Metalchocobo/minu-bench-scale/docs/mechanical/prototype-affordability/ready-made-frames.md

# Telai commerciali per un solo prototipo economico

La candidatura principale corrente è il [gruppo T130 illustrato nelle immagini fornite da Andrea](t130-assessment.md). Le opzioni sotto sono confronti alternativi; il prezzo completo del T130 resta da verificare.

Ricerca del 7 settembre 2026. Obiettivo: eliminare i quattro pezzi CNC del Concept 02 e usare componenti gia prodotti. Nessun acquisto o contatto con venditori; nessun nuovo CAD.

**Esito:** esistono staffe singole da circa 15 GBP e gruppi cinesi con cella proposti intorno a 28 USD, ma non e stato verificato un kit economico completo da 200-250 mm, con cella, base, piatto e tutte le quote d'innesto certe. Non e corretto sommare il prezzo di una sola staffa e presentarlo come costo dell'intera struttura. Le tre opzioni sotto indicano cosa si puo effettivamente acquistare e cosa resta da accertare.

## 1. Staffa singola in ferro, 265 x 170 x 10 mm — la pista economica piu concreta

Prodotto: **Stable Iron Scale Pan Support Bracket for Digital and Platform Scales**, venditore teamsome, spedizione da Shenzhen. [Inserzione eBay 366608848932](https://www.ebay.co.uk/itm/366608848932).

| Voce | Evidenza disponibile |
|---|---|
| Minimo | **1 pezzo**; descrizione confezione: una staffa |
| Prezzo letto | **14,84 GBP per un pezzo**, offerta a scadenza; 3 disponibili nella pagina consultata |
| Spedizione | La sessione mostrava 3,11 GBP verso un CAP estero preimpostato: **non e un preventivo per l'Italia** |
| Ingombro | **265 x 170 x 10 mm** dichiarati nella descrizione |
| Materiale | Ferro, finitura nera; spessore effettivo della lamiera non pubblicato |
| Incluso | Una staffa di supporto del piatto |
| Non elencati nella confezione | Cella, basamento inferiore, piatto, distanziali, viti, piedi |
| Quote mancanti | Interassi e diametri fori, piano d'appoggio cella, offset verticale, fissaggi piatto, geometria interna |
| Compatibilita | Nessun modello preciso di cella dichiarato; la compatibilita con Zemic L6D non e dimostrata |

La descrizione della **singola** staffa non specifica una portata numerica. L'[inserzione da quattro staffe dello stesso venditore](https://www.ebay.co.uk/itm/366609051880), con identico ingombro dichiarato, riporta 30 kg e prezzo letto 43,35 GBP per confezione: questo dato **non certifica** la portata della variante singola, ne identifica una cella compatibile. Le fotografie e un titolo commerciale non sostituiscono tale verifica.

Valutazione progettuale: e un ricambio plausibile per sostenere un piatto vicino a 280 x 200 senza fresare il carrier. Prima di progettargli intorno la scocca bisogna misurare la staffa e definire l'accoppiamento alla cella e la base inferiore. Al momento risolve potenzialmente **un pezzo** della catena di carico.

## 2. GALOCE GPB158-ZJ — gruppo cinese con staffa/cella, MOQ 1 da verificare sulla variante

[Prodotto Alibaba GPB158-ZJ, ID 1601389605861](https://www.alibaba.com/product-detail/GALOCE-GPB158-ZJ-Galoce-Single-Point_1601389605861.html), Xi'an Gavin Electronic Technology / GALOCE. Il link diretto e reale ma non ha restituito testo; prezzo e MOQ sono visibili nella [vetrina del fornitore su Alibaba](https://suppliers.alibaba.com/xian-gavin-electronic-technology-co-ltd_2813524503), sezione prodotti, non nella sintesi generata automaticamente della stessa pagina.

| Voce | Evidenza disponibile |
|---|---|
| Minimo mostrato | **1 set** nel prodotto della vetrina Alibaba; altri annunci Made-in-China della stessa famiglia richiedono 10 set, quindi il MOQ va riferito a questo link |
| Prezzo mostrato | **188,81 CNY/set** nella vetrina Alibaba; 28 USD/set in risultati commerciali della famiglia. Non costituisce un totale spedito in Italia |
| Configurazione | Articolo denominato GPB158-ZJ, presentato come single point con staffa; **contenuto della specifica variante non verificato integralmente** |
| Dimensioni certe correlate | Il produttore indica per la **sola cella GPB158** 150 x 38 x 22 mm e piattaforma massima 400 x 400 mm |
| Portata certa correlata | Il produttore indica GPB158 **60-300 kg**; non assumere una variante 30 o 50 kg dal titolo di altri annunci |
| Quote mancanti | Ingombro effettivo della staffa ZJ, interassi verso base/piatto, altezza, portata esatta selezionabile al prezzo, elenco viti e piedi |
| Piatto/base | Non verificati come inclusi; non chiamare questo articolo una piattaforma finita 250 x 250 |

Fonte primaria per le dimensioni della cella e i campi di carico: [GALOCE, soluzione per distributori automatici](https://www.galoce.com/Solutions/Automated-Vending-Machine-Weighing-Solution). Il limite di piattaforma della cella **non e la dimensione della staffa venduta**.

Valutazione: e la pista piu interessante per comprare insieme cella e supporto compatibili, evitando un accoppiamento inventato. Tuttavia la cella di questa famiglia e sovradimensionata rispetto a 20 kg utili e non promette accuratezza di 1 g. I dati mancanti impediscono di congelare un CAD o un costo totale affidabile.

## 3. Giropes BMS 30 kg 250 x 250 S — piattaforma completa, riferimento tecnico ma costo superiore

[ELEKTRONIKWERK, piattaforma BMS](https://elektronikwerk.de/en/products/wagebrucke-bms). Selezione desiderata: **BMS 30kg 250x250 S**.

| Voce | Evidenza disponibile |
|---|---|
| Minimo | Unita acquistabile a carrello; non e indicato un lotto industriale |
| Prezzo | Pagina generale **239 EUR + IVA**; **prezzo della variante 30 kg/250 x 250 non isolato**, non usarlo come preventivo della variante |
| Dimensioni | Piatto **250 x 250 mm**, portata nominale piattaforma 30 kg |
| Altezza | Famiglia di queste misure 52-70 mm con telaio verniciato; altezza della specifica variante da confermare |
| Incluso nella piattaforma descritta | Sottostruttura in acciaio verniciato, piatto inox, cella installata, piedi regolabili, livella, cavo 5 m |
| Display | Strumenti indicatori indicati come accessori/opzioni, non necessari per il progetto |
| Quote mancanti | Interfacce di fissaggio alla nuova scocca, disegno del telaio interno, tipo/esatto cablaggio della cella, prezzo e altezza della variante |
| Disponibilita | Pagina generale indica 6-7 giorni lavorativi; non verificata separatamente per variante e destinazione Italia |

Questo e un gruppo di pesatura gia realizzato nella taglia utile. Il costo visualizzato lo rende poco coerente con il prototipo minimo: rimane un confronto concreto con una struttura completa, evitando di confrontare una piattaforma finita con una sola staffa.

## Kit piccolo verificato, escluso dalla soluzione da 20 kg utili

[Handsontec ASS-1055](https://handsontec.com/index.php/product/load-cell-mounting-platform/): **5,50 USD**, un kit per lotto, indicato in stock. Include due piastre alluminio 5052 **100 x 100 x 3 mm**, quattro distanziali tondi da 6 mm, due viti M4x16 e due M5x16. [PDF del produttore](https://www.handsontec.com/dataspecs/alum-material/Load-Cell-Mouting-Kit.pdf). La cella non e inclusa. Il produttore indica celle 5/10/20 kg; non e stata trovata una versione 200 o 250 mm dello stesso kit. Aggiungere un piatto grande non dimostra rigidezza o resistenza eccentrica e una cella 20 kg non lascia margine per tara mobile oltre 20 kg utili.

## Decisione utile per il prossimo prototipo

La direzione economica e **riutilizzare un gruppo di pesatura gia completo**, oppure comprare una staffa commerciale e misurarla prima di disegnare gli innesti. Fra i componenti trovati, la staffa singola eBay e il ricambio a costo certo piu vicino all'ingombro; il GPB158-ZJ e la pista per un gruppo cella/supporto, con dettagli ancora incompleti. Nessuno dei due e gia verificato come sostituto completo dei quattro pezzi CNC.

Non sono state trasferite quote dal vecchio Concept 02 a questi articoli. Il precedente articolo AliExpress bloccato non e stato aperto o recuperato tramite altri canali. Non sono stati contattati venditori. Prezzi, stock, tasse e trasporto vanno riferiti alla variante esatta e alla destinazione del singolo ordine.
