Metalchocobo/minu-bench-scale/.codex-remote-attachments/01a0916e-df51-71a3-a685-71b7142ab0dd/86ad795f-8b1d-4ca9-9806-ef48b400f0ee/1-Photo-1.jpg

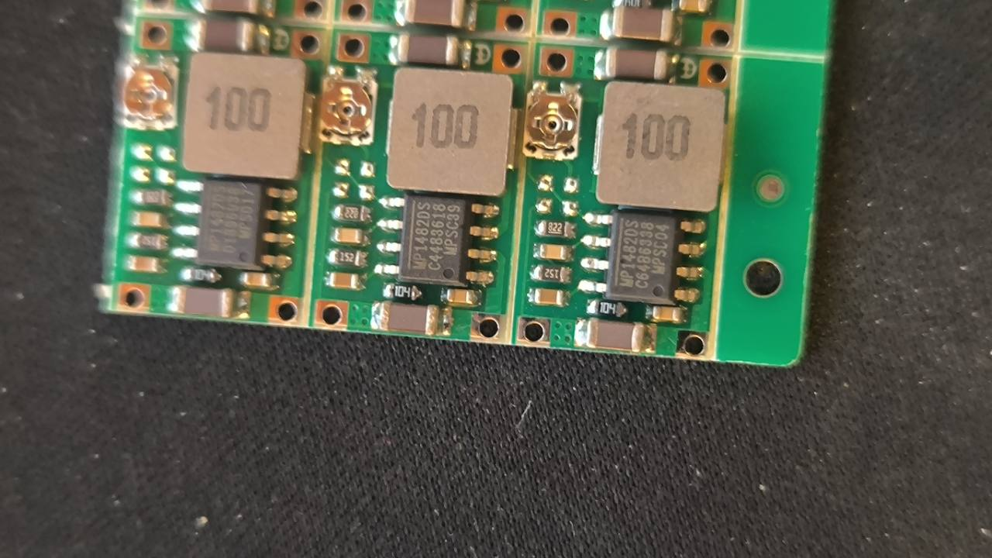
.codex-remote-attachments/01a0916e-df51-71a3-a685-71b7142ab0dd/86ad795f-8b1d-4ca9-9806-ef48b400f0ee/1-Photo-1.jpg
