Metalchocobo/minu-bench-scale/artifacts/mini360/01-alimentazione-mini360.png

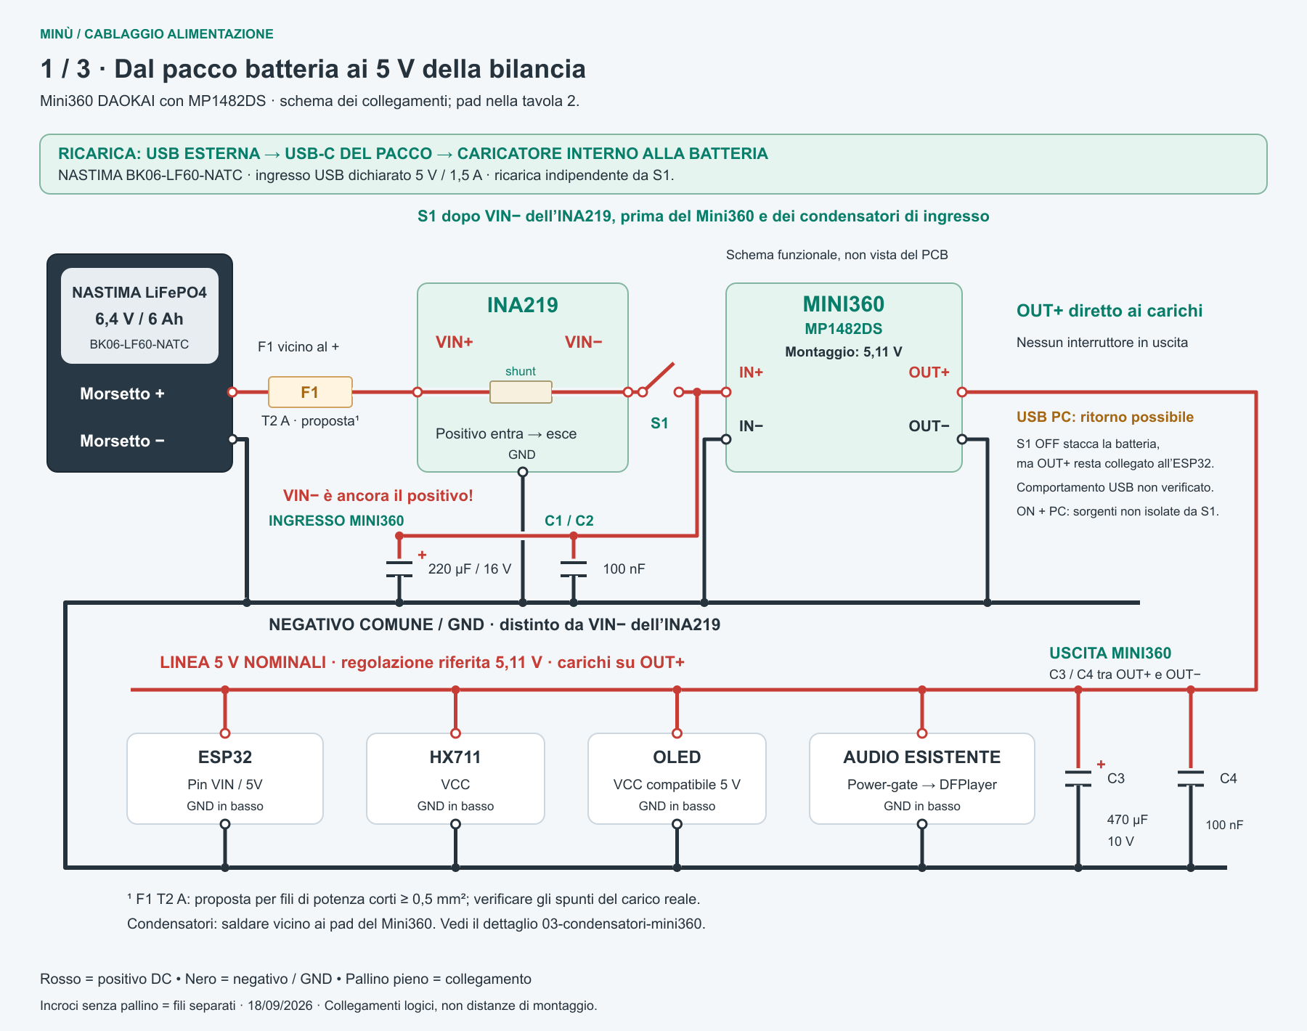
artifacts/mini360/01-alimentazione-mini360.png
