Metalchocobo/minu-bench-scale/artifacts/mini360/02-pad-regolazione-ina219.png

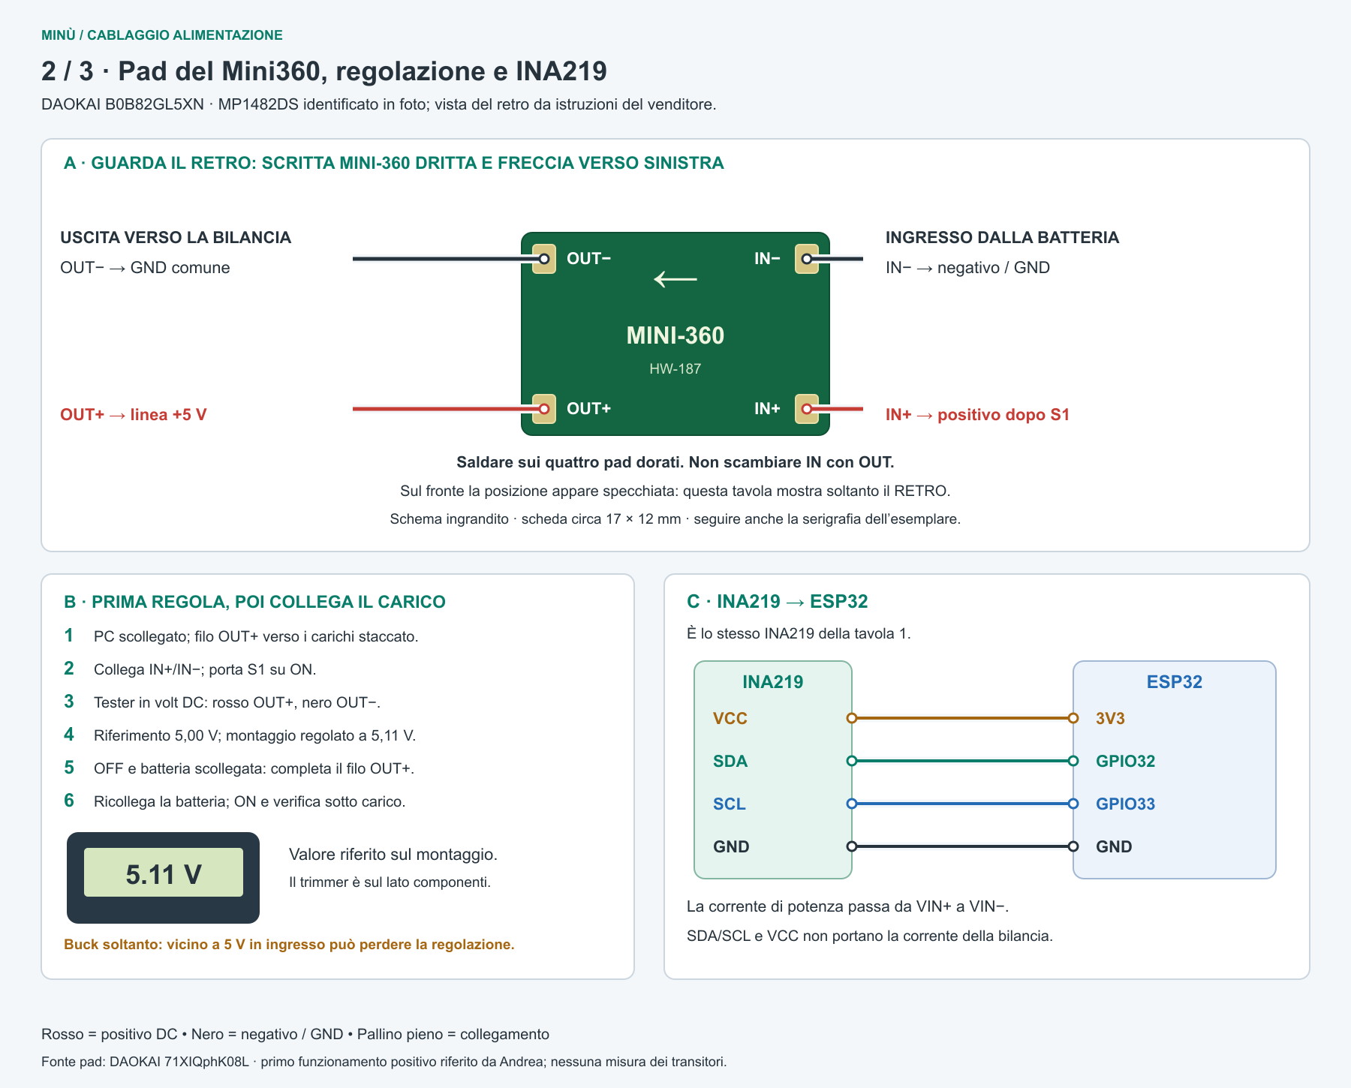
artifacts/mini360/02-pad-regolazione-ina219.png
