Metalchocobo/minu-bench-scale/artifacts/mini360/03-condensatori-mini360.png

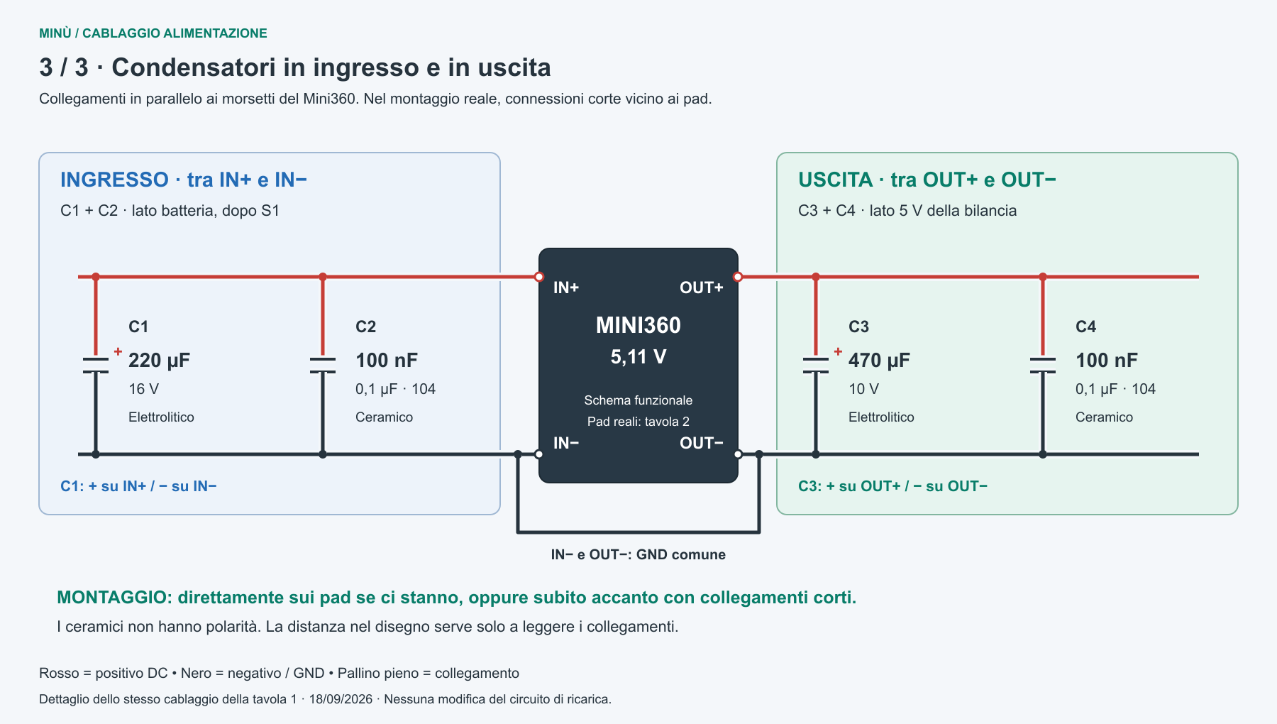
artifacts/mini360/03-condensatori-mini360.png
