Metalchocobo/minu-bench-scale/docs/mechanical/concept-01/concept-estetico.png

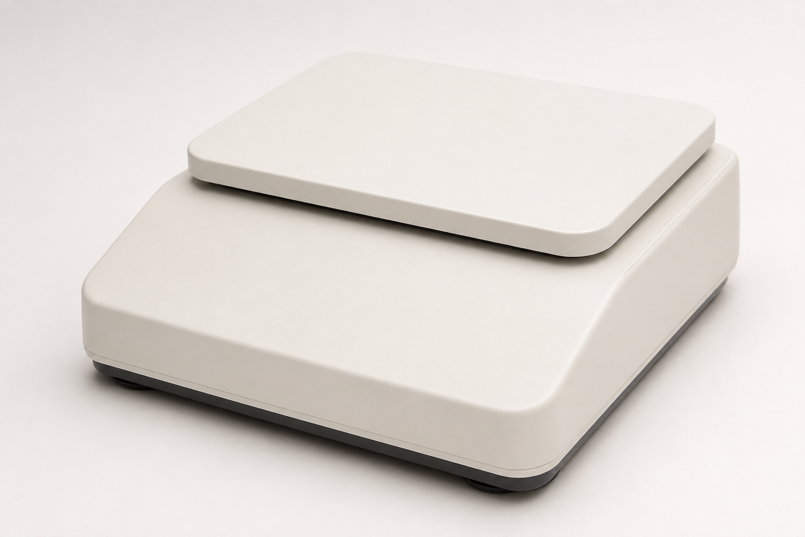
docs/mechanical/concept-01/concept-estetico.png
