Metalchocobo/minu-bench-scale/docs/mechanical/concept-02/sources/adafruit-1332-rear-reference.jpg

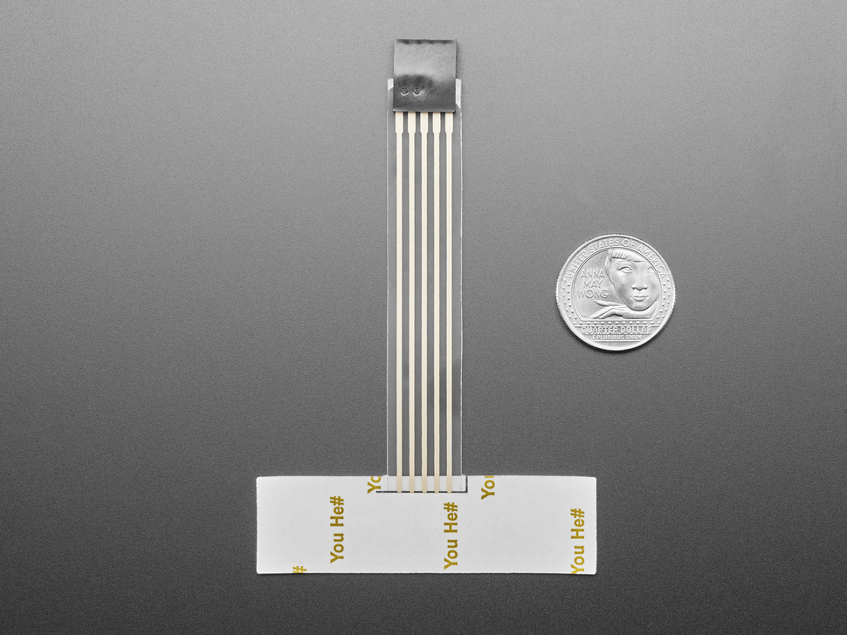
docs/mechanical/concept-02/sources/adafruit-1332-rear-reference.jpg
