Metalchocobo/minu-bench-scale/docs/mechanical/concept-02/sources/adafruit-6069-dimensions.jpg

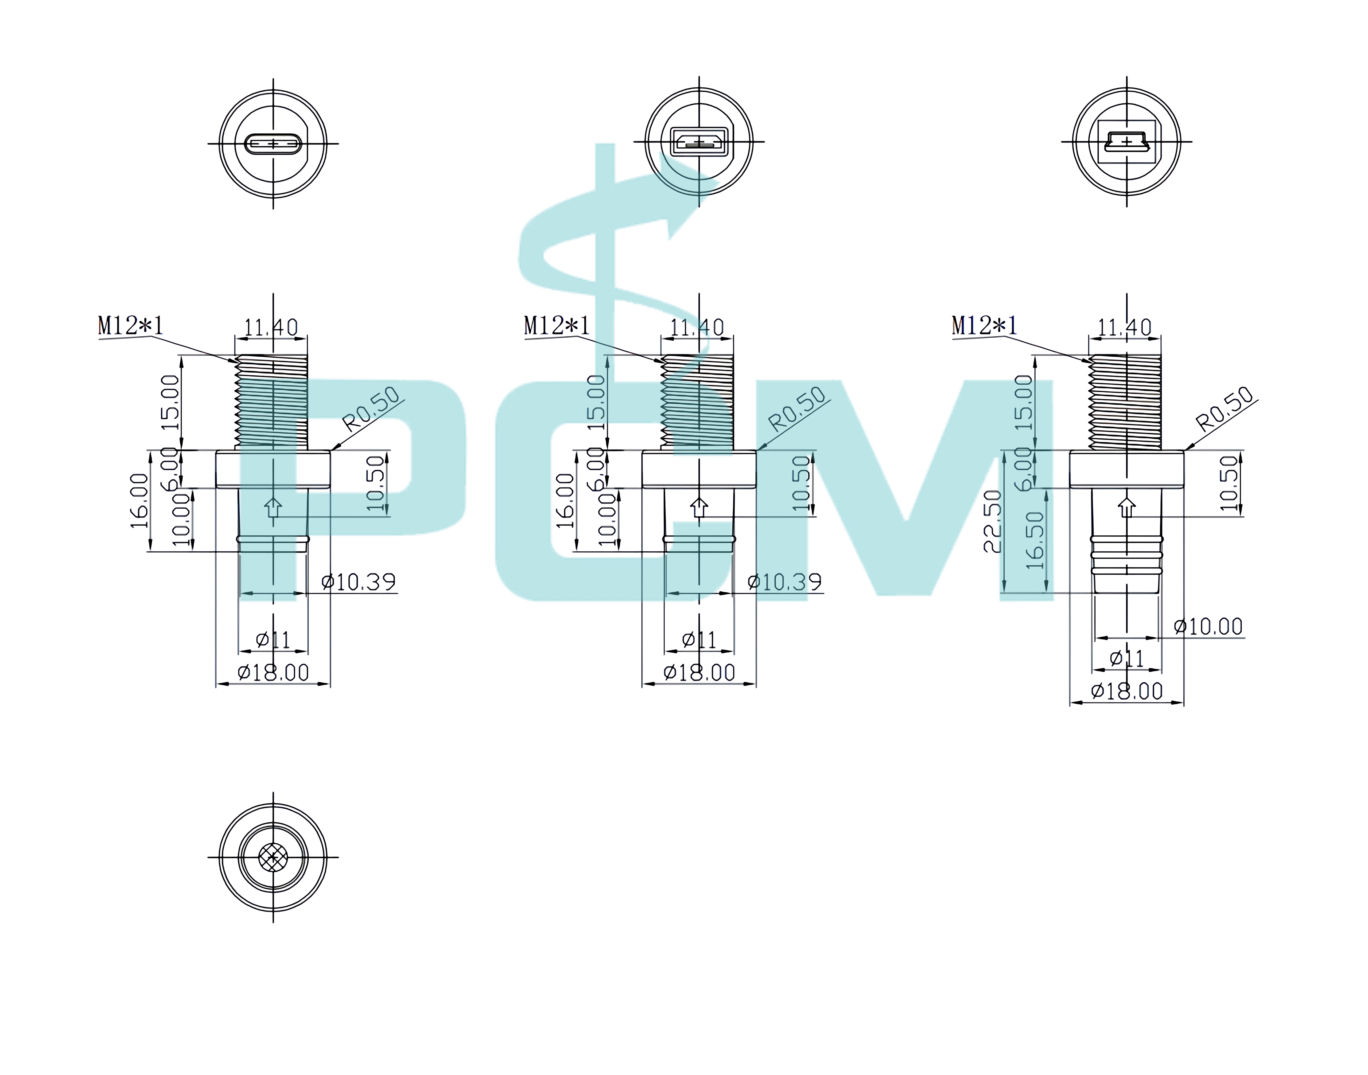
docs/mechanical/concept-02/sources/adafruit-6069-dimensions.jpg
