Metalchocobo/minu-bench-scale/docs/mechanical/concept-02/sources/Elesa-LX-AS-dimensions.png

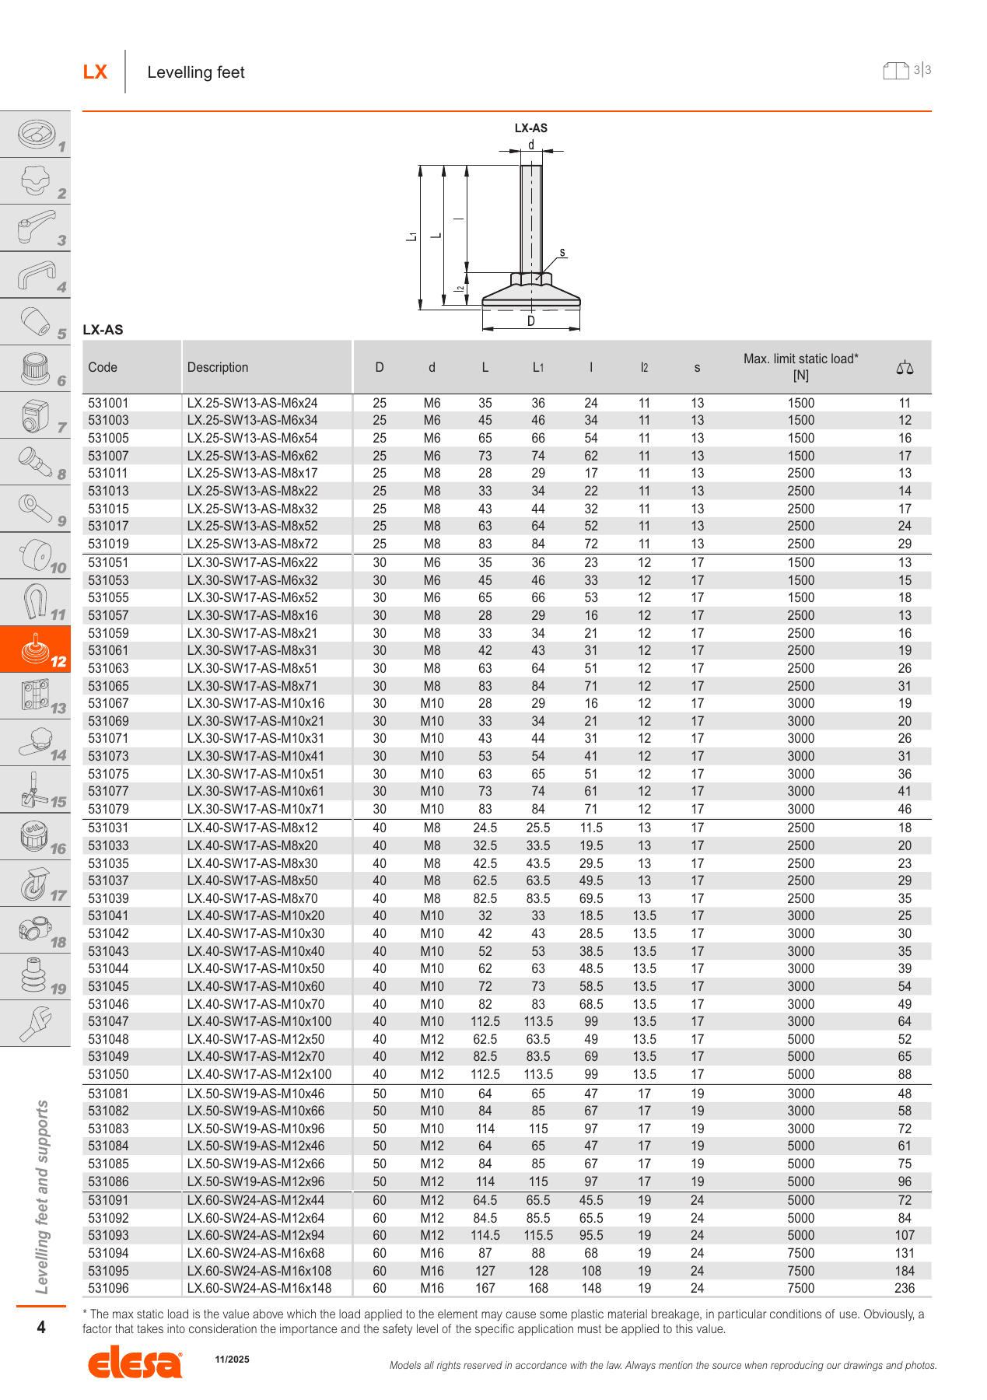
docs/mechanical/concept-02/sources/Elesa-LX-AS-dimensions.png
