Metalchocobo/minu-bench-scale/docs/mechanical/concept-02/sources/Zemic-L6D-dimensions.png

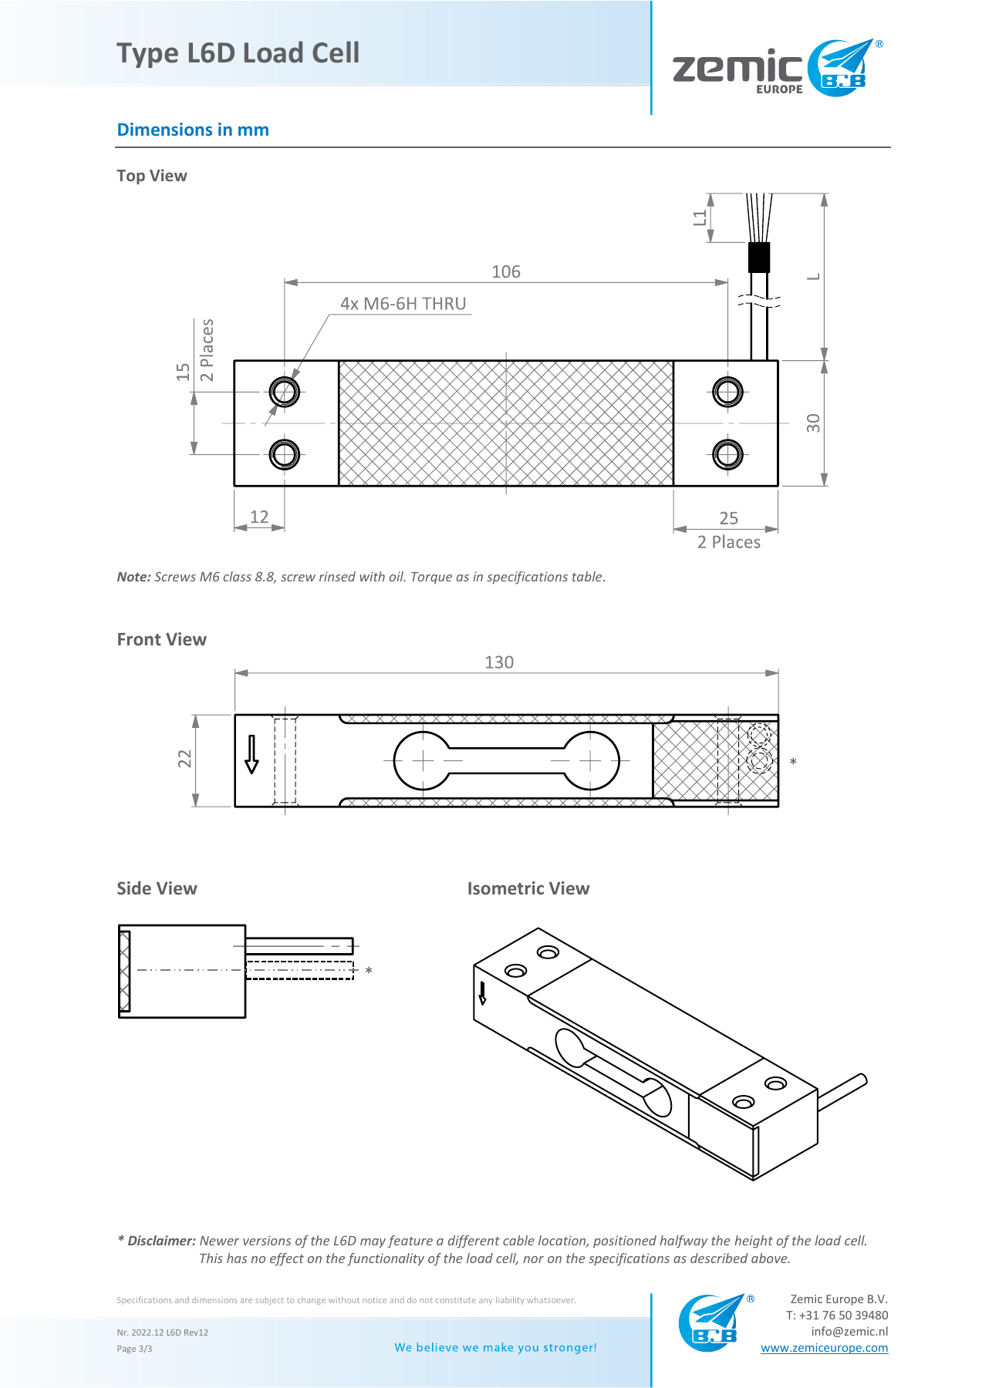
docs/mechanical/concept-02/sources/Zemic-L6D-dimensions.png
