Metalchocobo/minu-bench-scale/docs/mechanical/prototype-affordability/sources/t130-01-offer.png

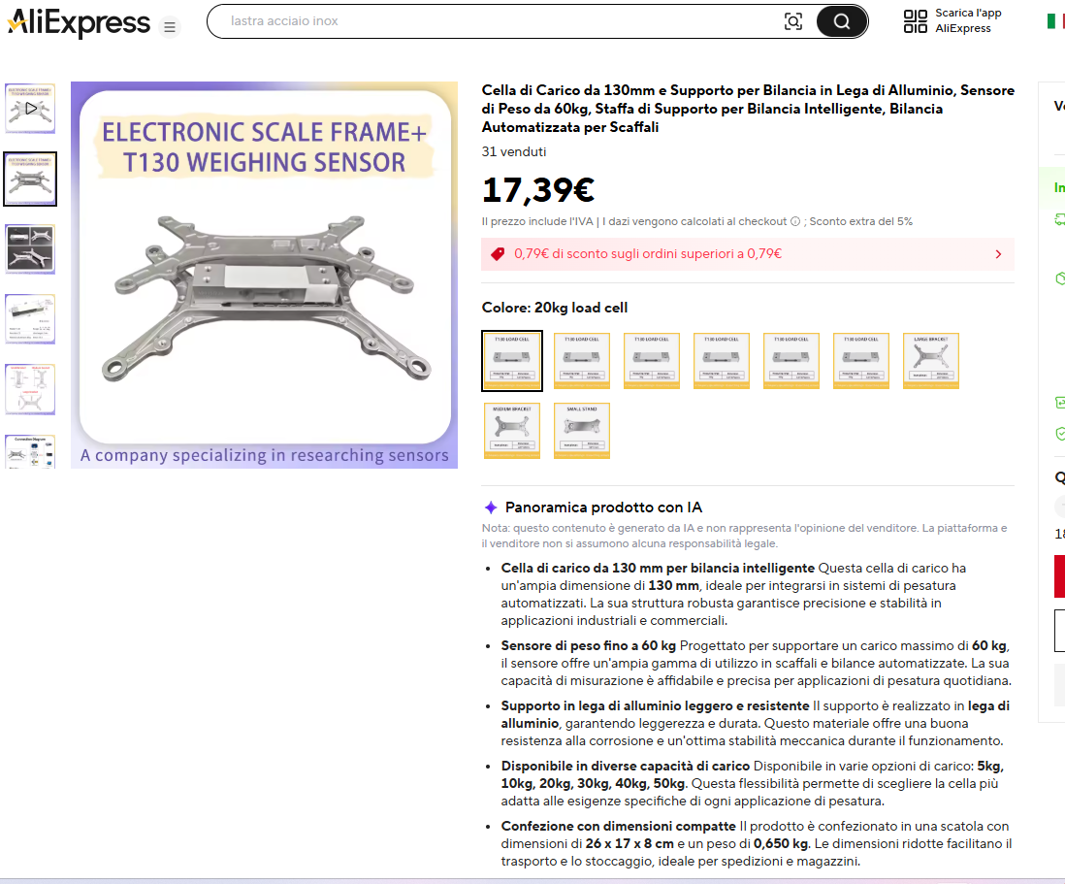
docs/mechanical/prototype-affordability/sources/t130-01-offer.png
