Metalchocobo/minu-bench-scale/docs/mechanical/prototype-affordability/sources/t130-02-brackets.png

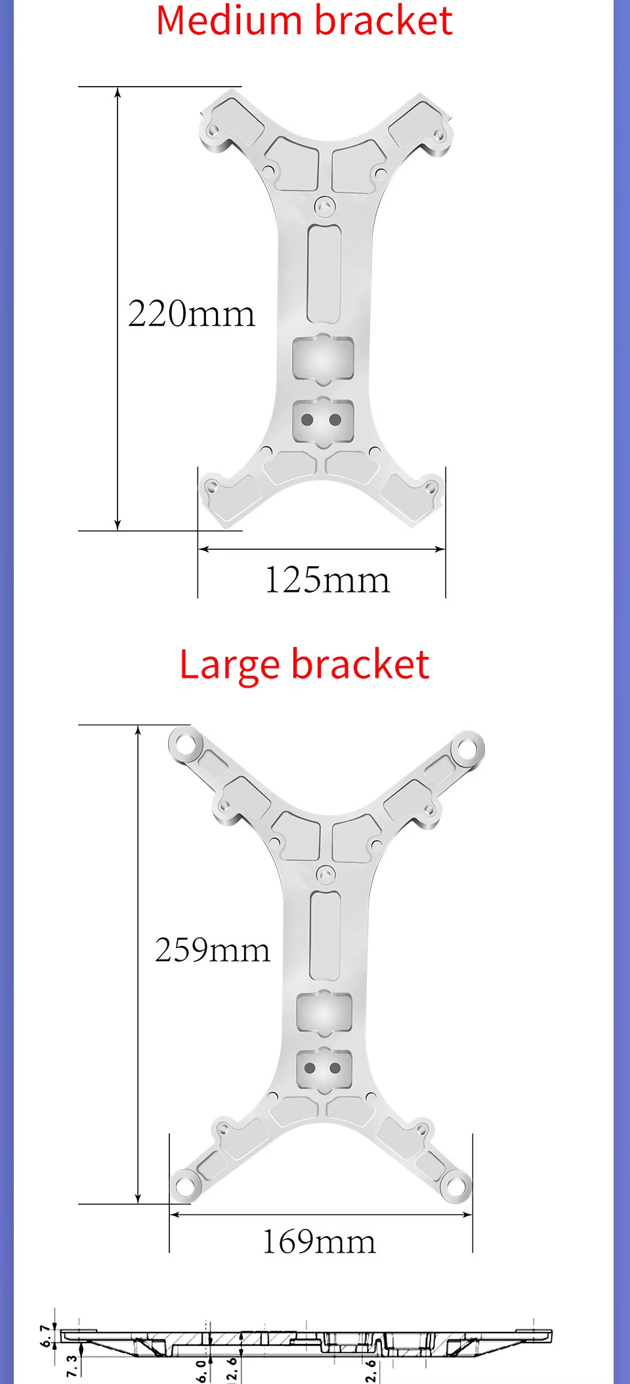
docs/mechanical/prototype-affordability/sources/t130-02-brackets.png
