Metalchocobo/minu-bench-scale/docs/mechanical/concept-02/step/plate_carrier_aluminium.step

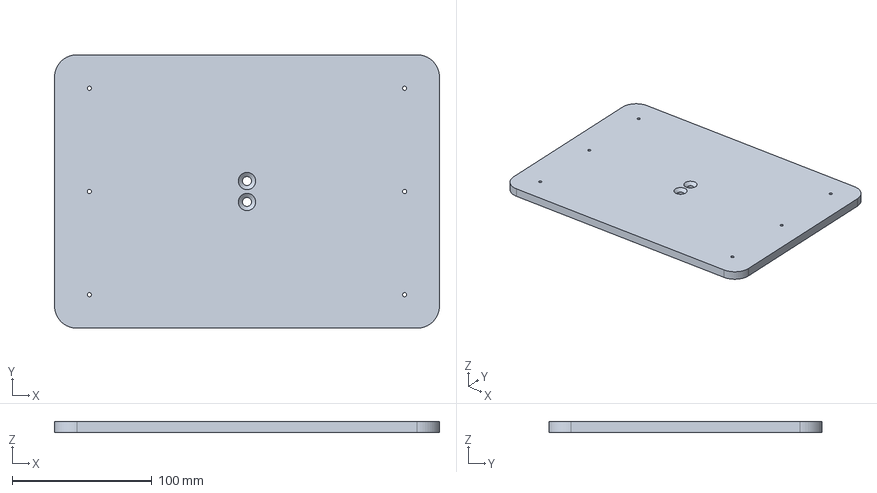
[picture p34: CAD file, 2026-09-19]
docs/mechanical/concept-02/step/plate_carrier_aluminium.step
276.0 x 196.0 x 8.00 mm
