Metalchocobo/minu-bench-scale/docs/mechanical/concept-02/step/plastic_pan.step

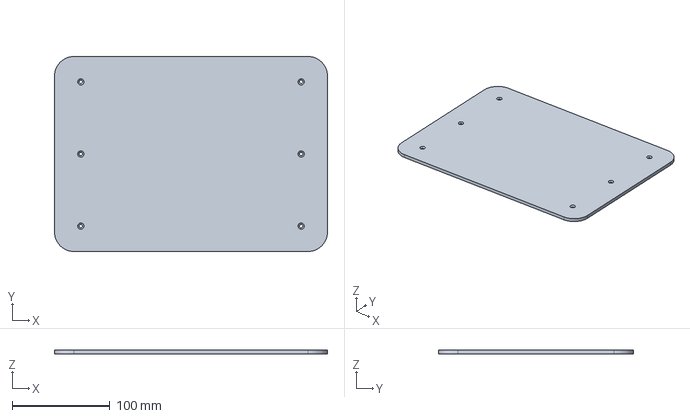
[picture p35: CAD file, 2026-09-19]
docs/mechanical/concept-02/step/plastic_pan.step
280.0 x 200.0 x 4.00 mm
