Metalchocobo/minu-bench-scale/docs/mechanical/concept-02/step/display_rear_bar_2.step

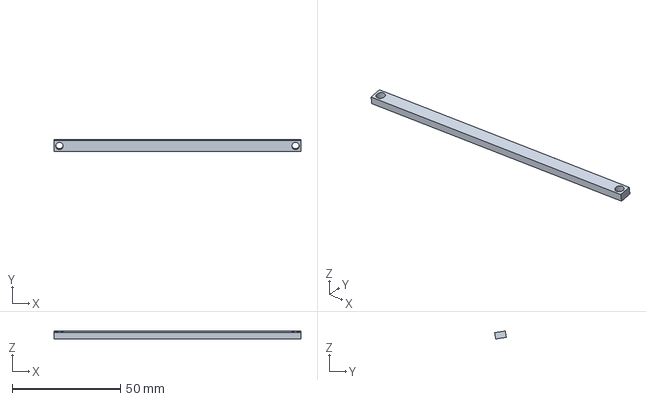
[picture p36: CAD file, 2026-09-19]
docs/mechanical/concept-02/step/display_rear_bar_2.step
114.0 x 5.40 x 3.73 mm
