Metalchocobo/minu-bench-scale/docs/mechanical/concept-02/step/keypad_hood_adhesive_1_3.step

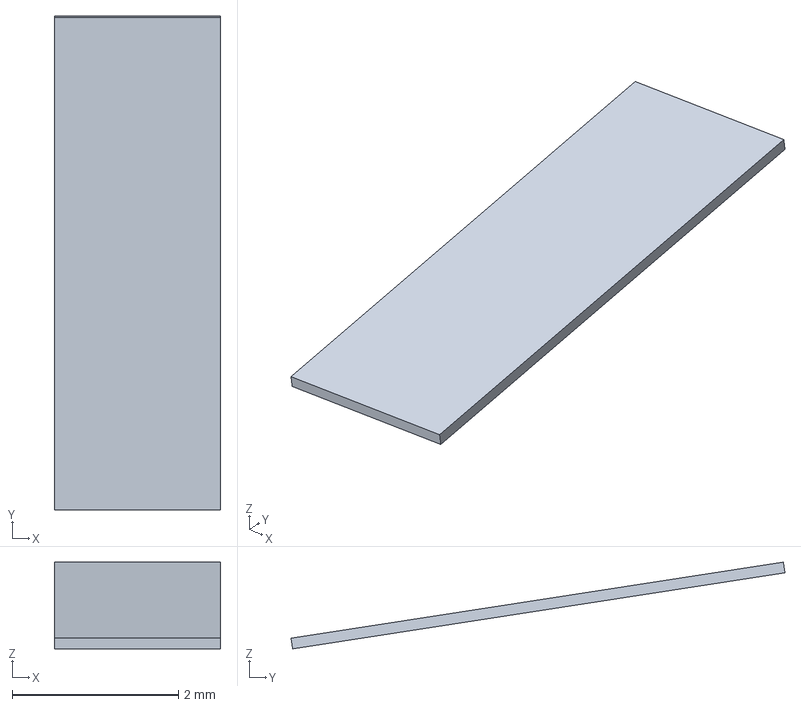
[picture p37: CAD file, 2026-09-19]
docs/mechanical/concept-02/step/keypad_hood_adhesive_1_3.step
2.00 x 5.95 x 1.04 mm
