Metalchocobo/minu-bench-scale/docs/mechanical/concept-02/step/base_aluminium.step

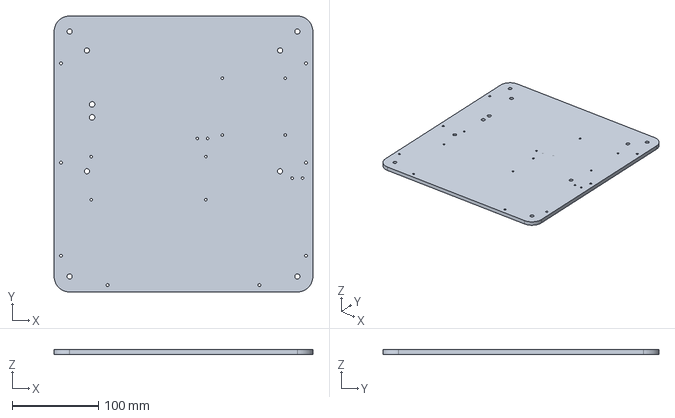
[picture p38: CAD file, 2026-09-19]
docs/mechanical/concept-02/step/base_aluminium.step
300.0 x 320.0 x 6.00 mm
