Metalchocobo/minu-bench-scale/docs/mechanical/concept-02/step/power_retaining_strap_1.step

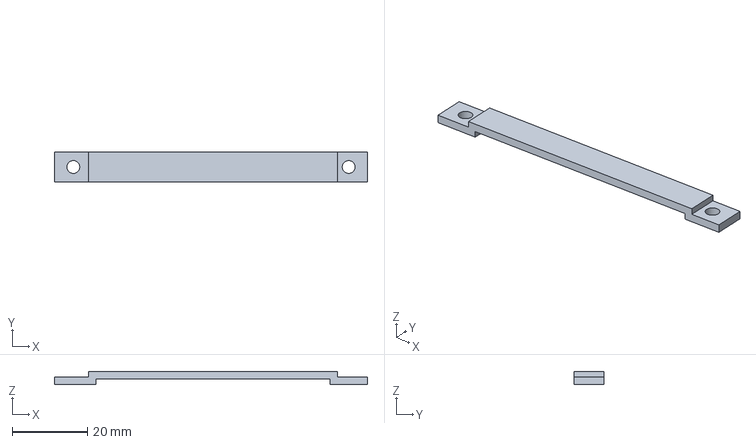
[picture p39: CAD file, 2026-09-19]
docs/mechanical/concept-02/step/power_retaining_strap_1.step
83.0 x 8.00 x 3.50 mm
