Metalchocobo/minu-bench-scale/docs/mechanical/concept-02/step/power_tray.step

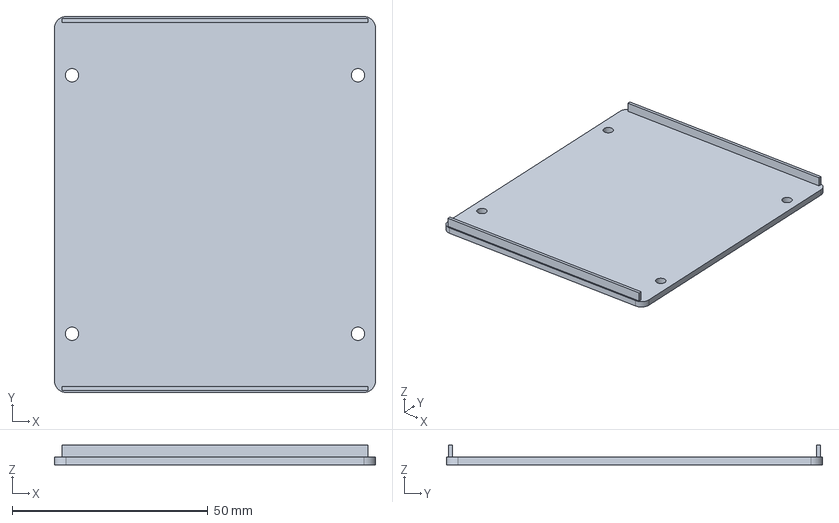
[picture p40: CAD file, 2026-09-19]
docs/mechanical/concept-02/step/power_tray.step
82.0 x 96.0 x 5.00 mm
