Metalchocobo/minu-bench-scale/docs/mechanical/concept-02/step/electronics_tray.step

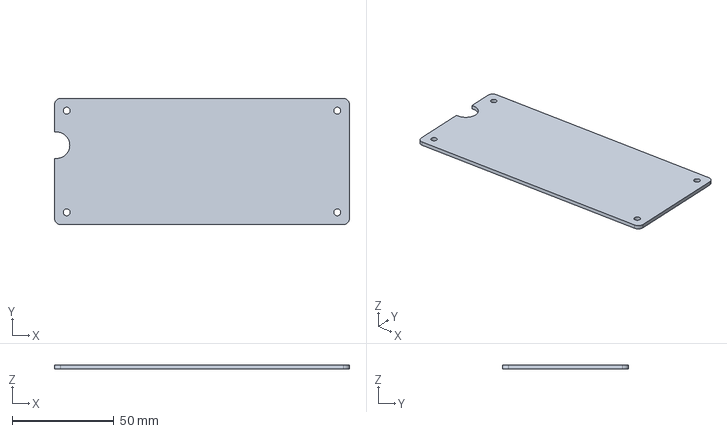
[picture p41: CAD file, 2026-09-19]
docs/mechanical/concept-02/step/electronics_tray.step
145.0 x 62.0 x 2.00 mm
