Metalchocobo/minu-bench-scale/docs/mechanical/concept-02/step/cable_clamp_upper_2.step

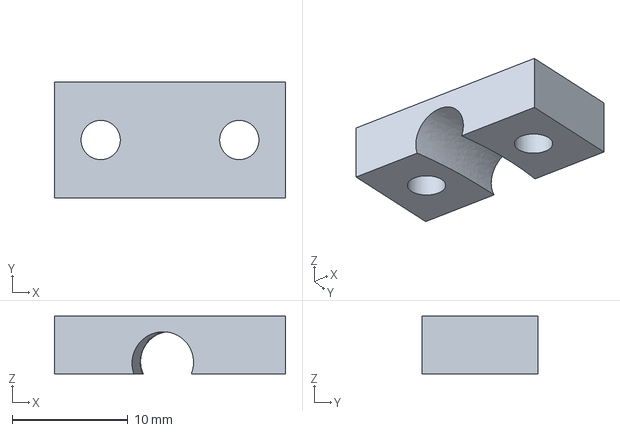
[picture p42: CAD file, 2026-09-19]
docs/mechanical/concept-02/step/cable_clamp_upper_2.step
20.0 x 10.0 x 5.00 mm
