Metalchocobo/minu-bench-scale/docs/mechanical/concept-02/step/keypad_hood_adhesive_2_1.step

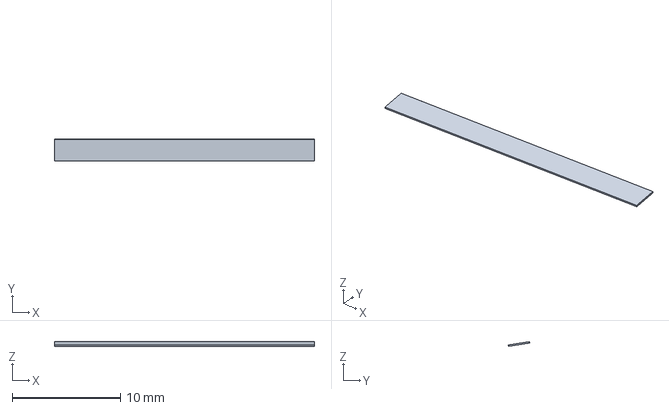
[picture p43: CAD file, 2026-09-19]
docs/mechanical/concept-02/step/keypad_hood_adhesive_2_1.step
24.0 x 2.00 x 0.434 mm
