Metalchocobo/minu-bench-scale/firmware/esp32_hx711_serial/net_ota_cloud.h

#pragma once

// Gestione WiFi + OTA + MQTT + Arduino Cloud per Minù Bench Scale
// NOTE:
//  - Di default è attivo solo WiFi + OTA via Arduino IDE.
//  - Arduino Cloud è disabilitato; abilitalo cambiando ENABLE_ARDUINO_CLOUD a 1
//    e aggiungendo thingProperties.h generato da Arduino Cloud nella stessa cartella.

// Abilita / disabilita i vari moduli
#define ENABLE_WIFI_OTA       1   // 1 = attiva WiFi + OTA
#define ENABLE_ARDUINO_CLOUD  0   // 1 = attiva Arduino Cloud (richiede librerie + thingProperties.h)
#define ENABLE_MQTT           1   // 1 = attiva client MQTT per integrazione gestionale

#if ENABLE_WIFI_OTA
  #include <WiFi.h>
  #include <ESPmDNS.h>
  #include <WiFiUdp.h>
  #include <ArduinoOTA.h>
  #include "wifi_store.h"
  #include "ota_store.h"
#endif

#if ENABLE_MQTT
  // Header-side size; mqttSetup/mqttReloadCreds also enforce it at runtime.
  // 640 covers the bounded owner envelope and the diagnostic status payload.
  #define MQTT_MAX_PACKET_SIZE 640
  #include <WiFiClientSecure.h>
  #include <PubSubClient.h>
  #include <ArduinoJson.h>
  #include "mqtt_store.h"
#endif

#if ENABLE_ARDUINO_CLOUD
  #include <ArduinoIoTCloud.h>
  #include <Arduino_ConnectionHandler.h>
  #include "thingProperties.h"
#endif

// ========================= MQTT CONFIG =========================
#if ENABLE_MQTT
  // Host, username e password NON sono nel codice: si configurano via seriale
  // e vengono salvati in NVS (persistono tra aggiornamenti firmware).
  // Comandi: mqtt set "host" "user" "pass", mqtt creds, mqtt clear, mqtt apply
  #define MQTT_PORT       8883          // MQTTS (TLS)
  #define MQTT_FW_VERSION "1.5.2"
  #define MQTT_SCALE_NAME "Minu Bench Scale"  // Nome visibile nel browser
#endif

namespace Net {

#if ENABLE_WIFI_OTA
  // Inizializza WiFi STA (NON BLOCCANTE)
  void wifiSetup();

  // Sospende WiFi/OTA (prima di light-sleep)
  void wifiSuspend();

  // Ripristina WiFi dopo wake
  void wifiResume();

  // Ricarica credenziali da NVS e riavvia tentativi
  void wifiReloadCredsAndRestart();

  // Numero di credenziali configurate
  uint8_t wifiCredCount();

  // Configura OTA (registra handler)
  void otaSetup(const char* hostname = "minu-bench-scale");

  // True se OTA update in corso
  bool isOtaInProgress();
#endif

#if ENABLE_MQTT
  // Inizializza MQTT (da chiamare dopo wifiSetup)
  void mqttSetup();

  // Sospende MQTT (prima di light-sleep)
  void mqttSuspend(const char* state = "sleeping");

  // True se connesso al broker MQTT
  bool isMqttConnected();
  bool isMqttConnectInProgress();

  // Stage a confirm for the active command. Session-aware commands stay active
  // until the browser acknowledges the generated response_id.
  bool mqttConfirmActiveCommand(const char* expectedUuid, float actualWeight,
                                char* responseIdOut = nullptr,
                                size_t responseIdOutSize = 0);

  // Stage/publish a skip for the active command.
  bool mqttSkipActiveCommand();

  // A confirm_request is queued by the MQTT callback and consumed by the main
  // loop so the remote action follows the exact same ENTER path as the keypad.
  bool mqttPopConfirmRequest();

  // Transient request state. Neither state advances the Manager UI: only the
  // durable confirm response and its application ACK complete a weighing.
  void mqttMarkConfirmRequestStaged();
  void mqttFailConfirmRequest(const char* reason);

  // Stage/publish an undo receipt before a reversible remote stack entry is
  // removed locally. Session-aware only; the RAM outbox retries until ACK.
  bool mqttStageUndo(const char* uuid, uint32_t productId,
                     const char* undoOfResponseId, const char* sessionId);

  // Restituisce il scale_id (MAC formattato)
  const char* getScaleId();

  // Raw command presence is kept separate from actionability so an MQTT
  // disconnect cannot accidentally turn a remote command into a standalone
  // weigh. Connection-aware commands are actionable only while the exact
  // browser owner lease is fresh.
  bool   isMqttCommandActive();
  bool   isMqttCommandActionable();
  bool   isMqttResponsePending();
  // A pending response remains immutable and retries in background, but it
  // stops locking the physical operator after the remote consumer detaches or
  // the bounded delivery window expires.
  bool   isMqttResponseOperatorLocked();
  bool   isMqttLocalFallbackActive();
  // True only while a fresh Manager owner is attached and local fallback is
  // not active. This is intentionally separate from broker connectivity.
  bool   isMqttManagerAttached();
  // Physical TARE/ENTER always win over a stalled durable delivery. The
  // existing outbox remains immutable while subsequent work becomes local.
  bool   mqttDetachForLocalInput();
  float  getMqttTargetWeight();
  const char* getMqttCommandUuid();
  const char* getMqttCommandName();
  const char* getMqttCommandSessionId();
  const char* getMqttCommandConnectionId();
  const char* getMqttCommandId();
  const char* getMqttLastSessionId();
  uint32_t getMqttCommandProductId();

  // True once for every weigh activation or clear that changes active state.
  bool mqttPopActivity();

  // True once after the browser ACKs a durable undo REST commit.
  bool mqttPopUndoAck();

  // True once when the Manager quarantines an undo after committing an
  // incident. The staged local marker is discarded without restoring stack.
  bool mqttPopUndoReject();

  // True once when an undo was already restored locally after detach and the
  // Manager later quarantines it. Caller must invalidate local history and
  // require an operator weight/tare check; never apply another restore.
  bool mqttPopDetachedUndoReject();

  // True once when a committed confirm is quarantined. rollbackSafe is true
  // only if the response was still operator-locked when rejected; the caller
  // must additionally prove the exact response is the newest stack entry.
  bool mqttPopConfirmReject(char* responseIdOut, size_t responseIdOutSize,
                            bool* rollbackSafe);

  // Cross-layer safety gate after a detached undo incident. While set, MQTT
  // stays operationally local and cannot expose/ACK an actionable command.
  // Only a successfully applied physical TARE may clear it.
  void mqttSetTareRequired(bool required);

  // Records whether consuming mqttPopDetachedUndo() actually restored/popped
  // the local entry. Kept until the outbox reaches a terminal ACK/reject.
  void mqttReportDetachedUndoApplied(bool applied);

  // True once when an undo outbox becomes detached. The main loop applies the
  // already-requested local restore immediately; a later ACK must not apply it
  // a second time after local work has resumed.
  bool mqttPopDetachedUndo();

  // Ritorna true una sola volta se MQTT si è disconnesso (per buzzer x2 nel .ino)
  bool mqttPopDisconnectBeep();

  // Ritorna true una sola volta quando arriva un nuovo comando weigh
  bool mqttPopCommandRxBeep();

  // Ricarica credenziali MQTT da NVS e riconnette (senza reboot)
  void mqttReloadCreds();

  // True se le credenziali MQTT sono configurate in NVS
  bool isMqttConfigured();
#endif

#if ENABLE_ARDUINO_CLOUD
  // Inizializza Arduino Cloud
  void cloudSetup();
#endif

  // Da chiamare nel loop principale
  void update();

} // namespace Net
