Metalchocobo/minu-bench-scale/firmware/esp32_hx711_serial/battery_monitor.h

#pragma once

#include <Arduino.h>

enum BatteryLevel {
  BATT_LEVEL_FULL = 0,
  BATT_LEVEL_GOOD,
  BATT_LEVEL_LOW,
  BATT_LEVEL_CRITICAL,
  BATT_LEVEL_EMPTY
};

struct BatteryStatus {
  float voltage_V;     // Tensione batteria filtrata (V)
  float current_mA;    // Filtered load-branch current; USB charging bypasses the shunt.
  BatteryLevel level;  // Livello batteria (4 step)
  bool charging;       // Voltage-based UI indication, not a power-protection signal.
  bool valid;          // true only when the latest attempted read is valid
  uint32_t lastValidMs;
};

// Da chiamare dopo che il bus I2C è stato inizializzato (Wire.begin(...))
void battery_init();

// true se l'INA219 è stato trovato e inizializzato correttamente
bool battery_is_available();

// Da chiamare nel loop principale, passando millis()
void battery_update(uint32_t nowMs);

// Restituisce l'ultimo stato calcolato (copia per valore)
BatteryStatus battery_get_status();

// True only while the latest attempted sample is valid and recent enough.
bool battery_has_fresh_sample(uint32_t nowMs);

// Stampa su Serial una riga di debug leggibile
void battery_debug_print(const BatteryStatus &st);
