Metalchocobo/minu-bench-scale/firmware/esp32_hx711_serial/buzzer.h

#pragma once
#include <Arduino.h>

void buzzerInit();

void buzzerBootMelody();  // fanfara di boot

void buzzerKeyClick();    // click tasto
void buzzerOk();          // beep conferma
void buzzerError();       // doppio beep errore
void buzzerWarn();        // beep avviso (batteria scarica)
void buzzerMqttRx();      // beep distintivo ricezione comando weigh
